Han-ZenX/CORE/docs/references/A7_Lite_硬件资料/照片/A7_Lite功能接口.png

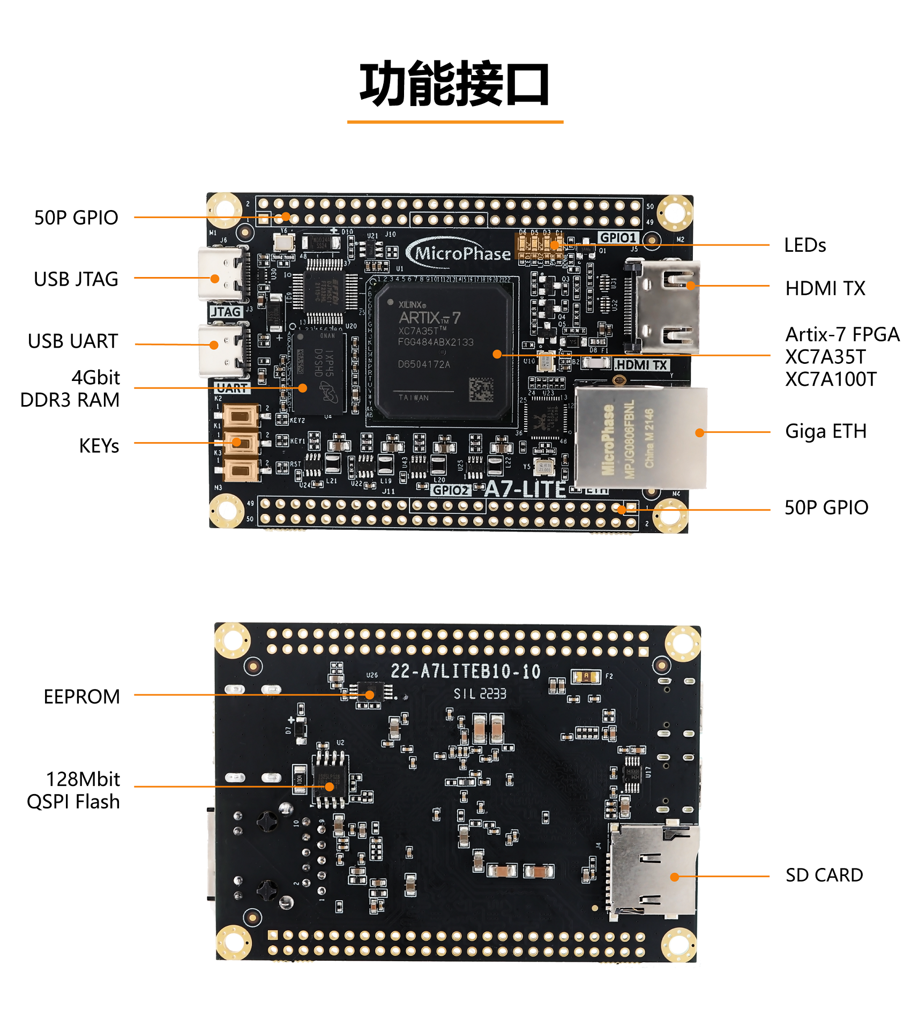
docs/references/A7_Lite_硬件资料/照片/A7_Lite功能接口.png
