Han-ZenX/CORE/docs/references/参考核心板1-1.jpg

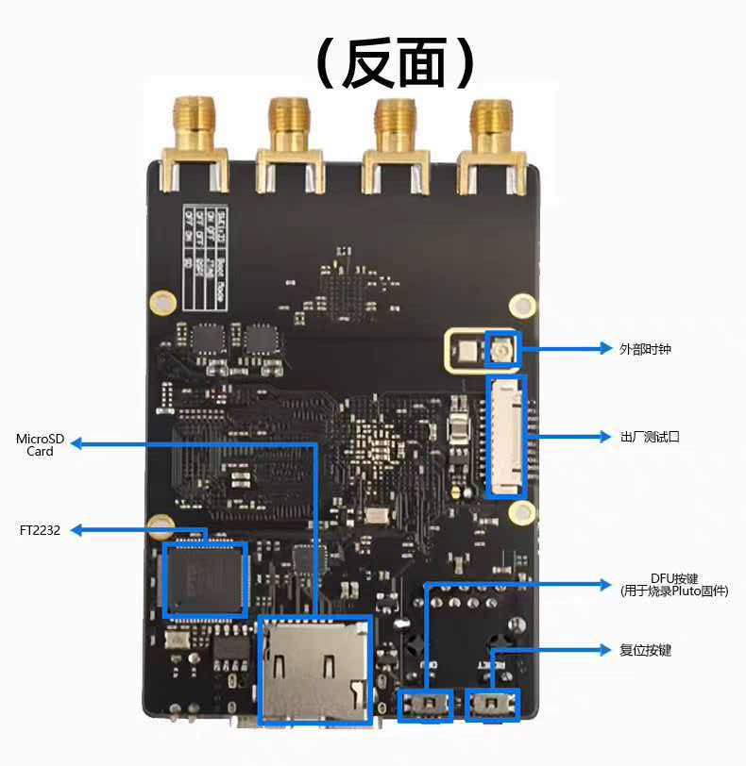
docs/references/参考核心板1-1.jpg
