Han-ZenX/CORE/docs/references/参考核心板3.jpg

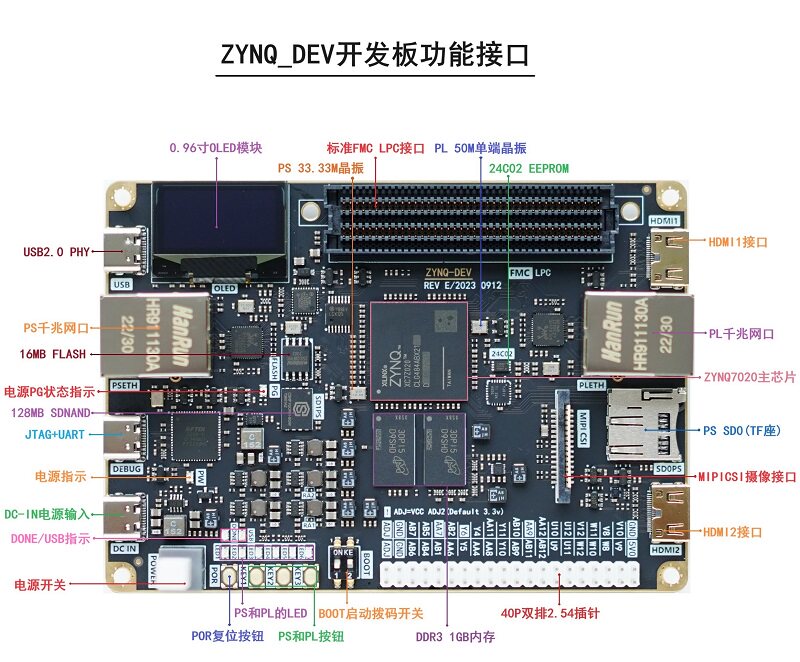
docs/references/参考核心板3.jpg
