Han-ZenX/CORE/hardware/schematic/v1.0/CORE/Comm_Periph.kicad_sch

## KiCad design hardware/schematic/v1.0/CORE/Comm_Periph.kicad_sch (2026-10-03)

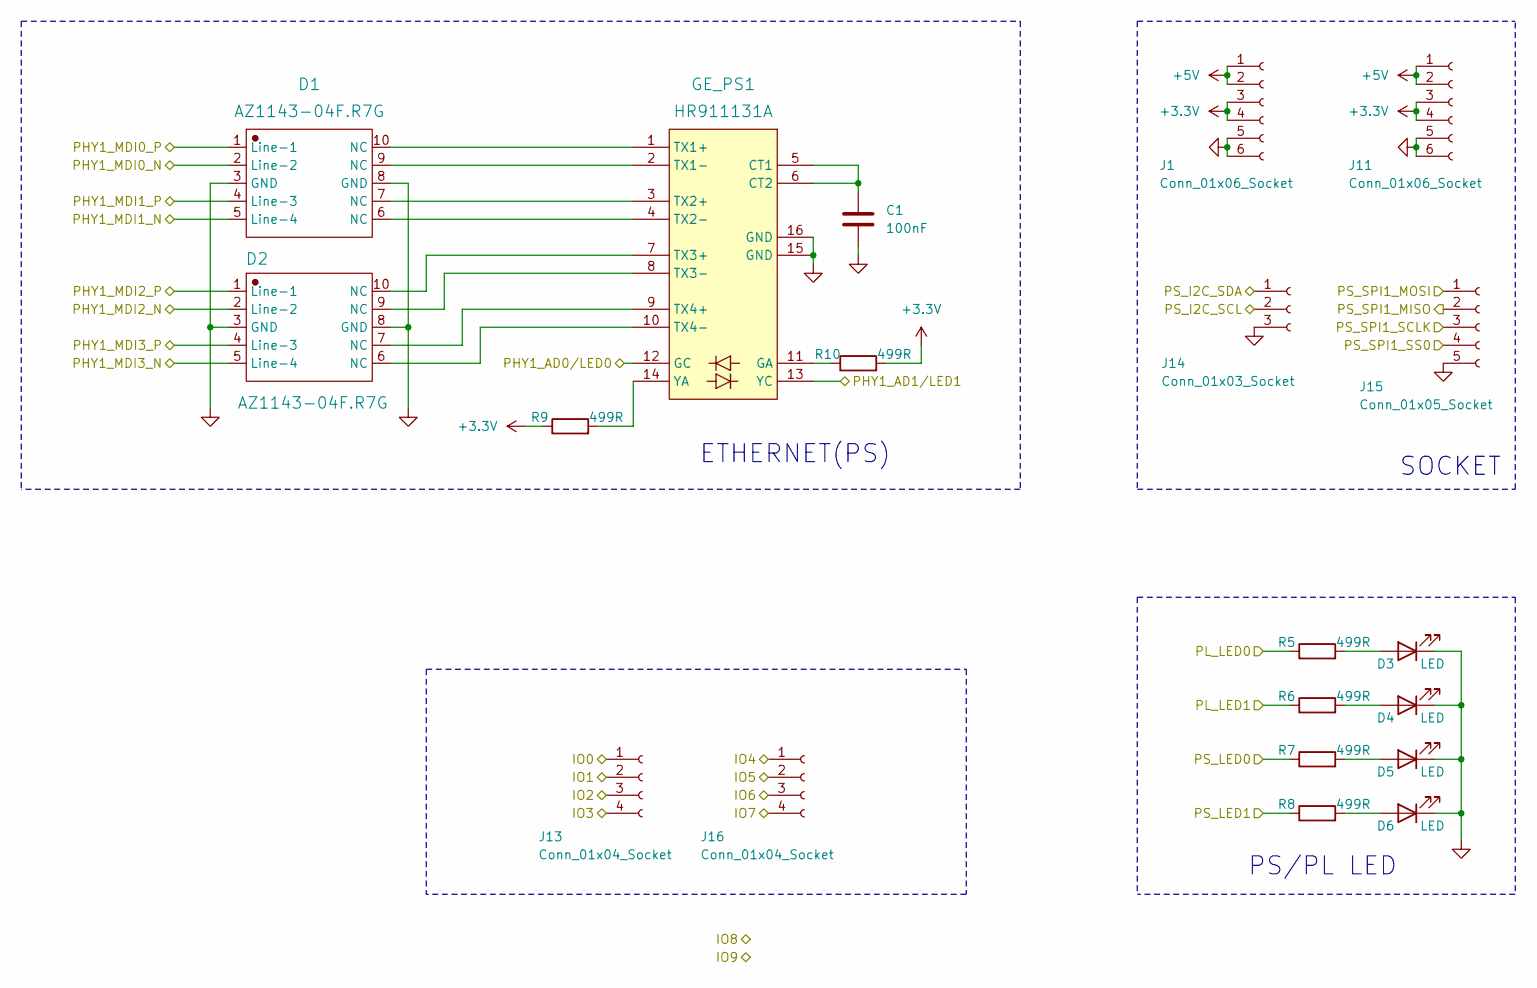
[picture p84: schematic Comm_Periph.kicad_sch]

Parts:
C1: 100nF; C_0402_1005Metric
D1, D2: AZ1143-04F.R7G; DFN2510P10E
D3, D4, D5, D6: LED; LED_0603_1608Metric
GE_PS1: HR911131A
J1, J11: Conn_01x06_Socket; PinHeader_1x06_P2.54mm_Vertical
J13, J16: Conn_01x04_Socket; PinHeader_1x04_P2.54mm_Vertical
J14: Conn_01x03_Socket; PinHeader_1x03_P2.54mm_Vertical
J15: Conn_01x05_Socket; PinHeader_1x05_P2.54mm_Vertical
R5, R6, R7, R8, R9, R10: 499R; R_0402_1005Metric

Connections:
+3.3V: J1.3, J1.4, J11.3, J11.4, R9.1, R10.2
+5V: J1.1, J1.2, J11.1, J11.2
GND: C1.2, D1.3 (GND), D1.8 (GND), D2.3 (GND), D2.8 (GND), D3.1 (K), D4.1 (K), D5.1 (K), D6.1 (K), GE_PS1.15 (GND), GE_PS1.16 (GND), J1.5, J1.6, J11.5, J11.6, J14.3, J15.5
IO0: J13.1
IO1: J13.2
IO2: J13.3
IO3: J13.4
IO4: J16.1
IO5: J16.2
IO6: J16.3
IO7: J16.4
unnamed: C1.1, GE_PS1.5 (CT1), GE_PS1.6 (CT2)
unnamed: D1.6 (NC), GE_PS1.4 (TX2-)
unnamed: D1.7 (NC), GE_PS1.3 (TX2+)
unnamed: D1.9 (NC), GE_PS1.2 (TX1-)
unnamed: D1.10 (NC), GE_PS1.1 (TX1+)
unnamed: D2.6 (NC), GE_PS1.10 (TX4-)
unnamed: D2.7 (NC), GE_PS1.9 (TX4+)
unnamed: D2.9 (NC), GE_PS1.8 (TX3-)
unnamed: D2.10 (NC), GE_PS1.7 (TX3+)
unnamed: D3.2 (A), R5.2
unnamed: D4.2 (A), R6.2
unnamed: D5.2 (A), R7.2
unnamed: D6.2 (A), R8.2
unnamed: GE_PS1.11 (GA), R10.1
unnamed: GE_PS1.14 (YA), R9.2
PHY1_AD0/LED0: GE_PS1.12 (GC)
PHY1_AD1/LED1: GE_PS1.13 (YC)
PHY1_MDI0_N: D1.2 (Line-2)
PHY1_MDI0_P: D1.1 (Line-1)
PHY1_MDI1_N: D1.5 (Line-4)
PHY1_MDI1_P: D1.4 (Line-3)
PHY1_MDI2_N: D2.2 (Line-2)
PHY1_MDI2_P: D2.1 (Line-1)
PHY1_MDI3_N: D2.5 (Line-4)
PHY1_MDI3_P: D2.4 (Line-3)
PL_LED0: R5.1
PL_LED1: R6.1
PS_I2C_SCL: J14.2
PS_I2C_SDA: J14.1
PS_LED0: R7.1
PS_LED1: R8.1
PS_SPI1_MISO: J15.2
PS_SPI1_MOSI: J15.1
PS_SPI1_SCLK: J15.3
PS_SPI1_SS0: J15.4

Notes on the sheet:
ETHERNET(PS)
PS/PL LED
SOCKET
