Han-ZenX/CORE/hardware/schematic/v1.0/CORE/Display.kicad_sch

## KiCad design hardware/schematic/v1.0/CORE/Display.kicad_sch (2026-09-08)

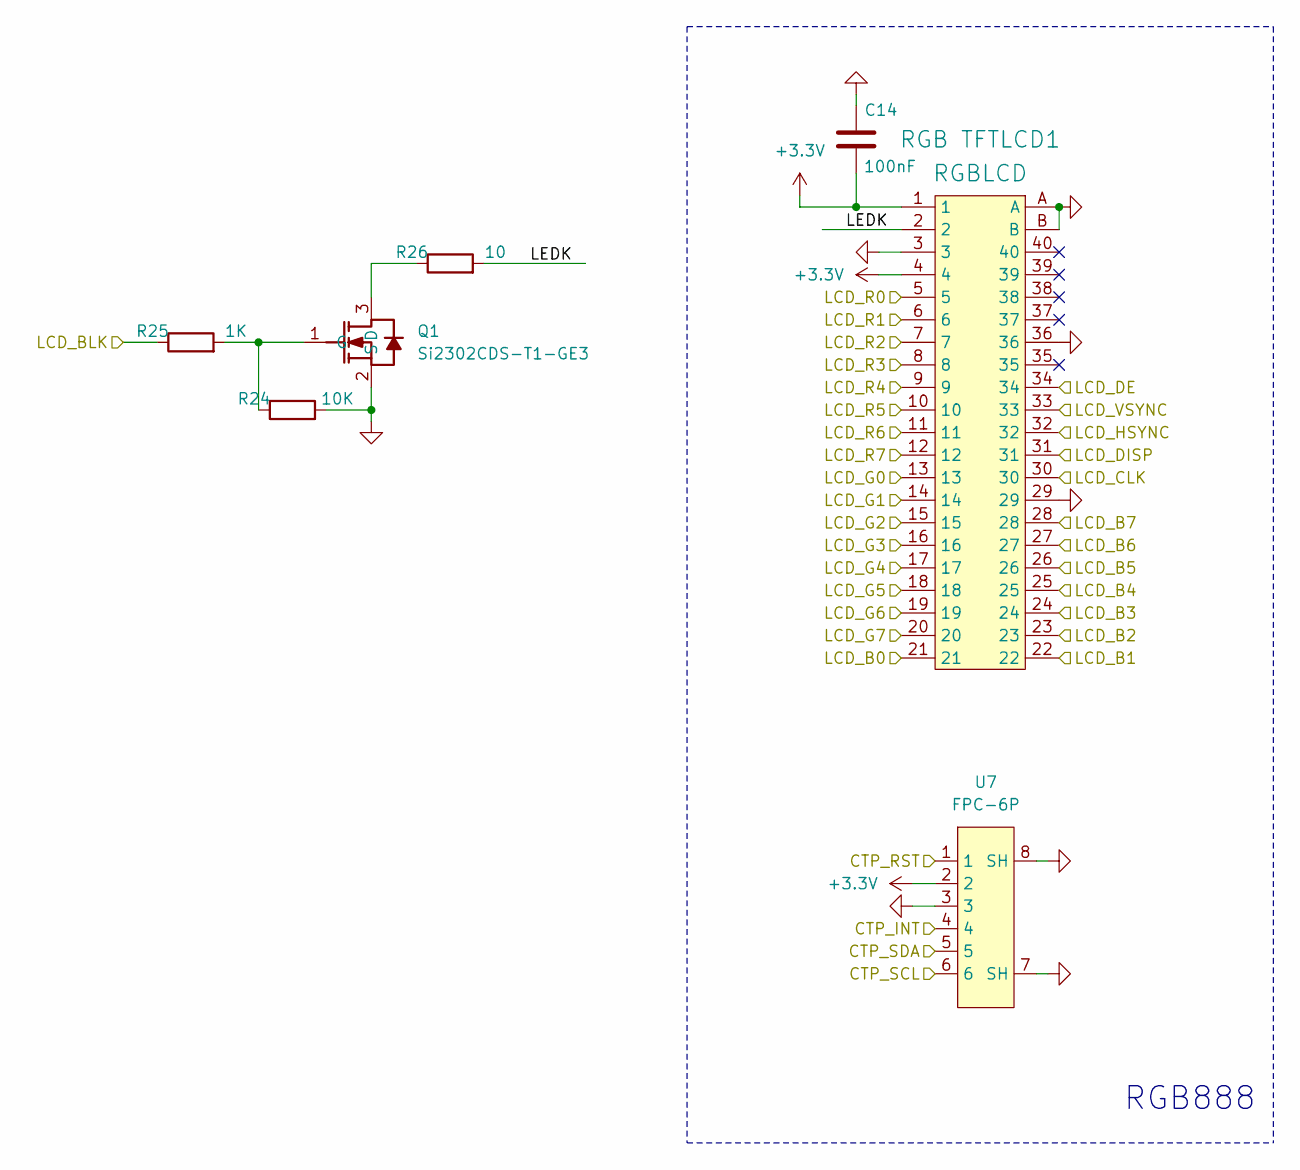
[picture p85: schematic Display.kicad_sch]

Parts:
C14: 100nF; C_0402_1005Metric
Q1: Si2302CDS-T1-GE3; Manufacturer Part Si2302CDS-T1-GE3; LCSC C10488
R24: 10K; R_0402_1005Metric
R25: 1K; R_0402_1005Metric
R26: 10; R_0402_1005Metric
RGB TFTLCD1: RGBLCD; FPC-TOP40
U7: FPC-6P

Connections:
+3.3V: C14.2, RGB TFTLCD1.1, RGB TFTLCD1.4, U7.2
CTP_INT: U7.4
CTP_RST: U7.1
CTP_SCL: U7.6
CTP_SDA: U7.5
GND: C14.1, Q1.2 (S), R24.2, RGB TFTLCD1.3, RGB TFTLCD1.29, RGB TFTLCD1.36, RGB TFTLCD1.A, RGB TFTLCD1.B, U7.3, U7.7 (SH), U7.8 (SH)
LCD_B0: RGB TFTLCD1.21
LCD_B1: RGB TFTLCD1.22
LCD_B2: RGB TFTLCD1.23
LCD_B3: RGB TFTLCD1.24
LCD_B4: RGB TFTLCD1.25
LCD_B5: RGB TFTLCD1.26
LCD_B6: RGB TFTLCD1.27
LCD_B7: RGB TFTLCD1.28
LCD_BLK: R25.1
LCD_CLK: RGB TFTLCD1.30
LCD_DE: RGB TFTLCD1.34
LCD_DISP: RGB TFTLCD1.31
LCD_G0: RGB TFTLCD1.13
LCD_G1: RGB TFTLCD1.14
LCD_G2: RGB TFTLCD1.15
LCD_G3: RGB TFTLCD1.16
LCD_G4: RGB TFTLCD1.17
LCD_G5: RGB TFTLCD1.18
LCD_G6: RGB TFTLCD1.19
LCD_G7: RGB TFTLCD1.20
LCD_HSYNC: RGB TFTLCD1.32
LCD_R0: RGB TFTLCD1.5
LCD_R1: RGB TFTLCD1.6
LCD_R2: RGB TFTLCD1.7
LCD_R3: RGB TFTLCD1.8
LCD_R4: RGB TFTLCD1.9
LCD_R5: RGB TFTLCD1.10
LCD_R6: RGB TFTLCD1.11
LCD_R7: RGB TFTLCD1.12
LCD_VSYNC: RGB TFTLCD1.33
LEDK: R26.2, RGB TFTLCD1.2
unnamed: Q1.1 (G), R24.1, R25.2
unnamed: Q1.3 (D), R26.1

Notes on the sheet:
RGB888
