Han-ZenX/CORE/hardware/schematic/v1.0/CORE/Power.kicad_sch

## KiCad design hardware/schematic/v1.0/CORE/Power.kicad_sch (2026-10-03)

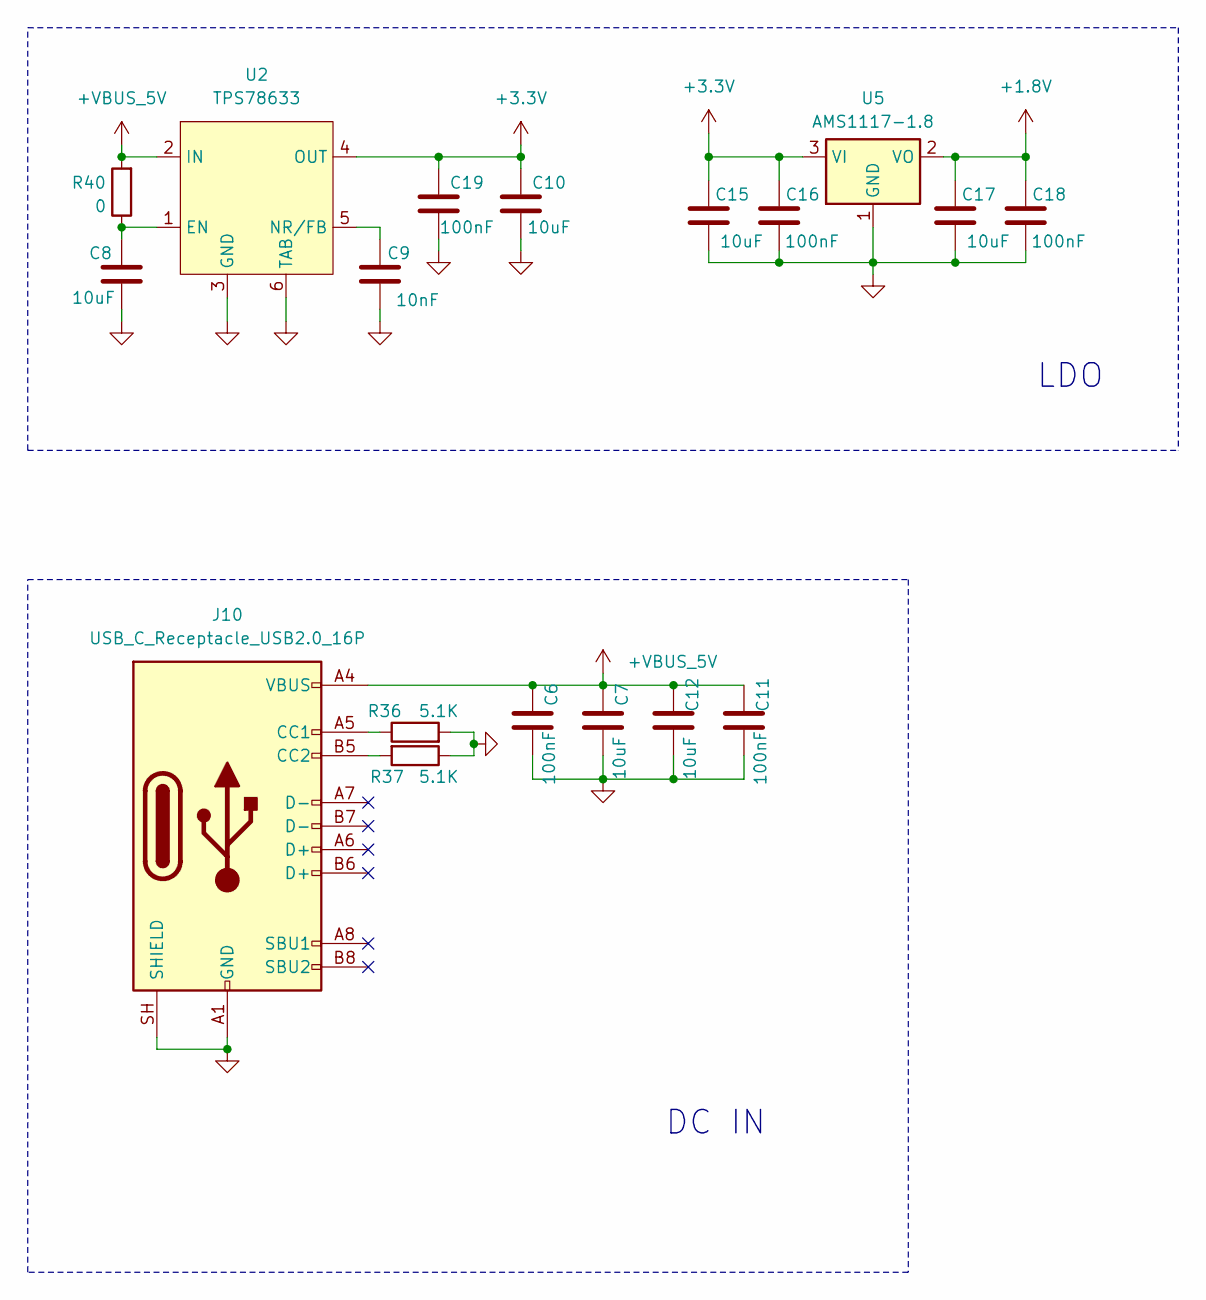
[picture p86: schematic Power.kicad_sch]

Parts:
C6, C11, C19: 100nF; C_0402_1005Metric
C7, C8, C10, C12, C15, C17: 10uF; C_0603_1608Metric
C9: 10nF; C_0402_1005Metric
C16, C18: 100nF; C_0603_1608Metric
J10: USB_C_Receptacle_USB2.0_16P; USB_C_Receptacle_Palconn_UTC16-G
R36, R37: 5.1K; R_0402_1005Metric
R40: 0; R_0402_1005Metric
U2: TPS78633; SOT-223-6
U5: AMS1117-1.8; SOT-223-3_TabPin2

Connections:
+1.8V: C17.1, C18.1, U5.2 (VO)
+3.3V: C10.2, C15.1, C16.1, C19.2, U2.4 (OUT), U5.3 (VI)
+VBUS_5V: C6.1, C7.1, C11.1, C12.1, J10.A4 (VBUS), J10.A9 (VBUS), J10.B4 (VBUS), J10.B9 (VBUS), R40.2, U2.2 (IN)
GND: C6.2, C7.2, C8.1, C9.1, C10.1, C11.2, C12.2, C15.2, C16.2, C17.2, C18.2, C19.1, J10.A1 (GND), J10.A12 (GND), J10.B1 (GND), J10.B12 (GND), J10.SH (SHIELD), R36.2, R37.1, U2.3 (GND), U2.6 (TAB), U5.1 (GND)
unnamed: C8.2, R40.1, U2.1 (EN)
unnamed: C9.2, U2.5 (NR/FB)
unnamed: J10.A5 (CC1), R36.1
unnamed: J10.B5 (CC2), R37.2

Notes on the sheet:
DC IN
LDO
