Han-ZenX/CORE/hardware/schematic/v1.0/CORE/Signal.kicad_sch

## KiCad design hardware/schematic/v1.0/CORE/Signal.kicad_sch (2026-10-02)

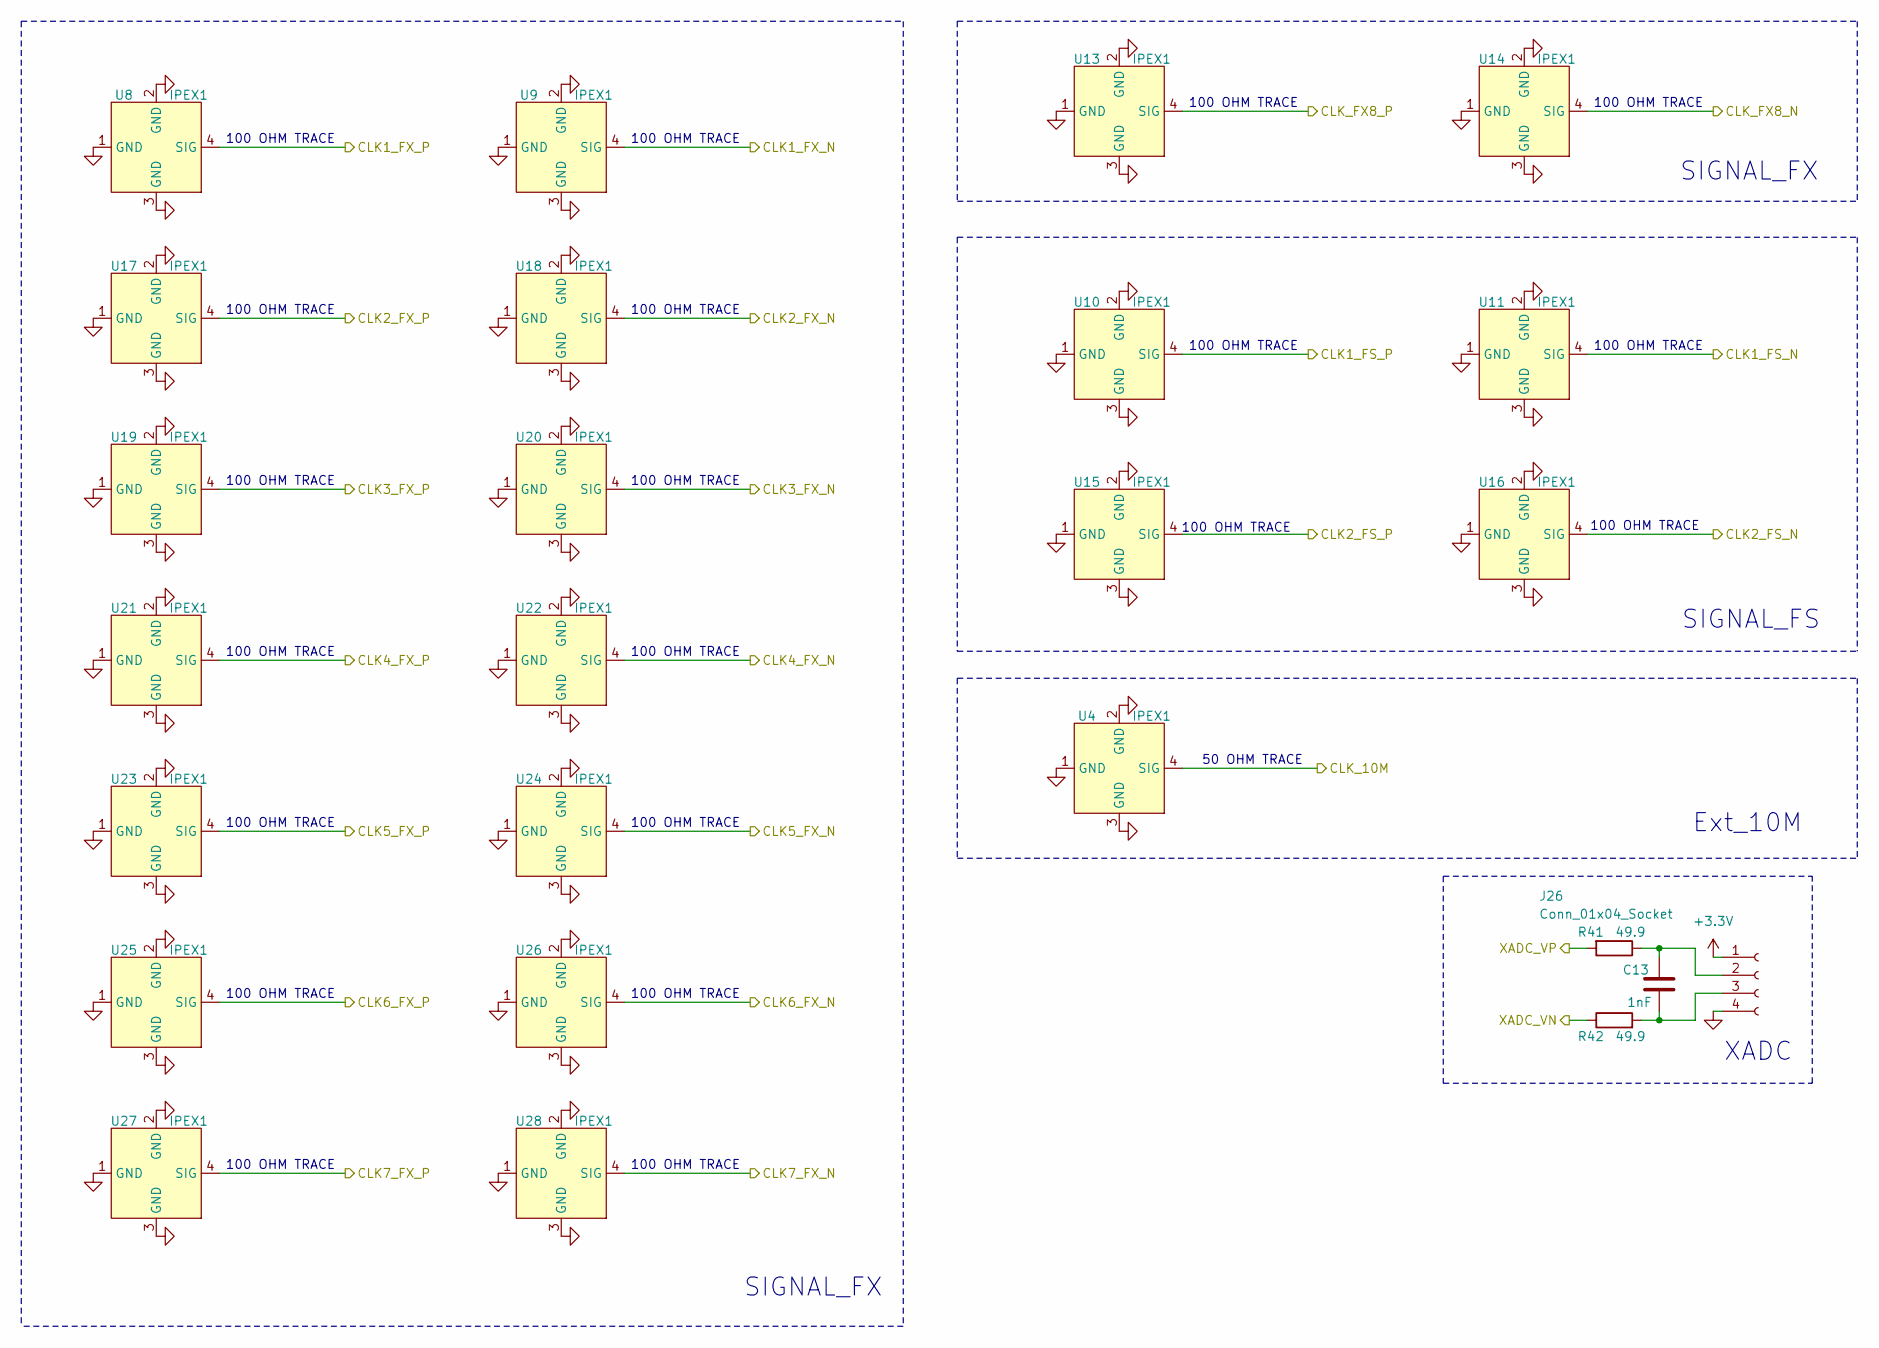
[picture p87: schematic Signal.kicad_sch]

Parts:
C13: 1nF; C_0402_1005Metric
J26: Conn_01x04_Socket; PinHeader_1x04_P2.54mm_Vertical
R41, R42: 49.9; R_0402_1005Metric
U4, U8, U9, U10, U11, U13, U14, U15, U16, U17, U18, U19, U20, U21, U22, U23, U24, U25, U26, U27, U28: IPEX1; JLC_IPEX-1

Connections:
+3.3V: J26.1
CLK1_FS_N: U11.4 (SIG)
CLK1_FS_P: U10.4 (SIG)
CLK1_FX_N: U9.4 (SIG)
CLK1_FX_P: U8.4 (SIG)
CLK2_FS_N: U16.4 (SIG)
CLK2_FS_P: U15.4 (SIG)
CLK2_FX_N: U18.4 (SIG)
CLK2_FX_P: U17.4 (SIG)
CLK3_FX_N: U20.4 (SIG)
CLK3_FX_P: U19.4 (SIG)
CLK4_FX_N: U22.4 (SIG)
CLK4_FX_P: U21.4 (SIG)
CLK5_FX_N: U24.4 (SIG)
CLK5_FX_P: U23.4 (SIG)
CLK6_FX_N: U26.4 (SIG)
CLK6_FX_P: U25.4 (SIG)
CLK7_FX_N: U28.4 (SIG)
CLK7_FX_P: U27.4 (SIG)
CLK_10M: U4.4 (SIG)
CLK_FX8_N: U14.4 (SIG)
CLK_FX8_P: U13.4 (SIG)
GND: J26.4, U4.1 (GND), U4.2 (GND), U4.3 (GND), U8.1 (GND), U8.2 (GND), U8.3 (GND), U9.1 (GND), U9.2 (GND), U9.3 (GND), U10.1 (GND), U10.2 (GND), U10.3 (GND), U11.1 (GND), U11.2 (GND), U11.3 (GND), U13.1 (GND), U13.2 (GND), U13.3 (GND), U14.1 (GND), U14.2 (GND), U14.3 (GND), U15.1 (GND), U15.2 (GND), U15.3 (GND), U16.1 (GND), U16.2 (GND), U16.3 (GND), U17.1 (GND), U17.2 (GND), U17.3 (GND), U18.1 (GND), U18.2 (GND), U18.3 (GND), U19.1 (GND), U19.2 (GND), U19.3 (GND), U20.1 (GND), U20.2 (GND), U20.3 (GND), U21.1 (GND), U21.2 (GND), U21.3 (GND), U22.1 (GND), U22.2 (GND), U22.3 (GND), U23.1 (GND), U23.2 (GND), U23.3 (GND), U24.1 (GND), U24.2 (GND), U24.3 (GND), U25.1 (GND), U25.2 (GND), U25.3 (GND), U26.1 (GND), U26.2 (GND), U26.3 (GND), U27.1 (GND), U27.2 (GND), U27.3 (GND), U28.1 (GND), U28.2 (GND), U28.3 (GND)
unnamed: C13.1, J26.2, R41.1
unnamed: C13.2, J26.3, R42.2
XADC_VN: R42.1
XADC_VP: R41.2

Notes on the sheet:
100 OHM TRACE
SIGNAL_FX
SIGNAL_FS
XADC
50 OHM TRACE
Ext_10M
