Han-ZenX/CORE/hardware/schematic/v1.0/CORE/Storage.kicad_sch

## KiCad design hardware/schematic/v1.0/CORE/Storage.kicad_sch (2026-10-03)

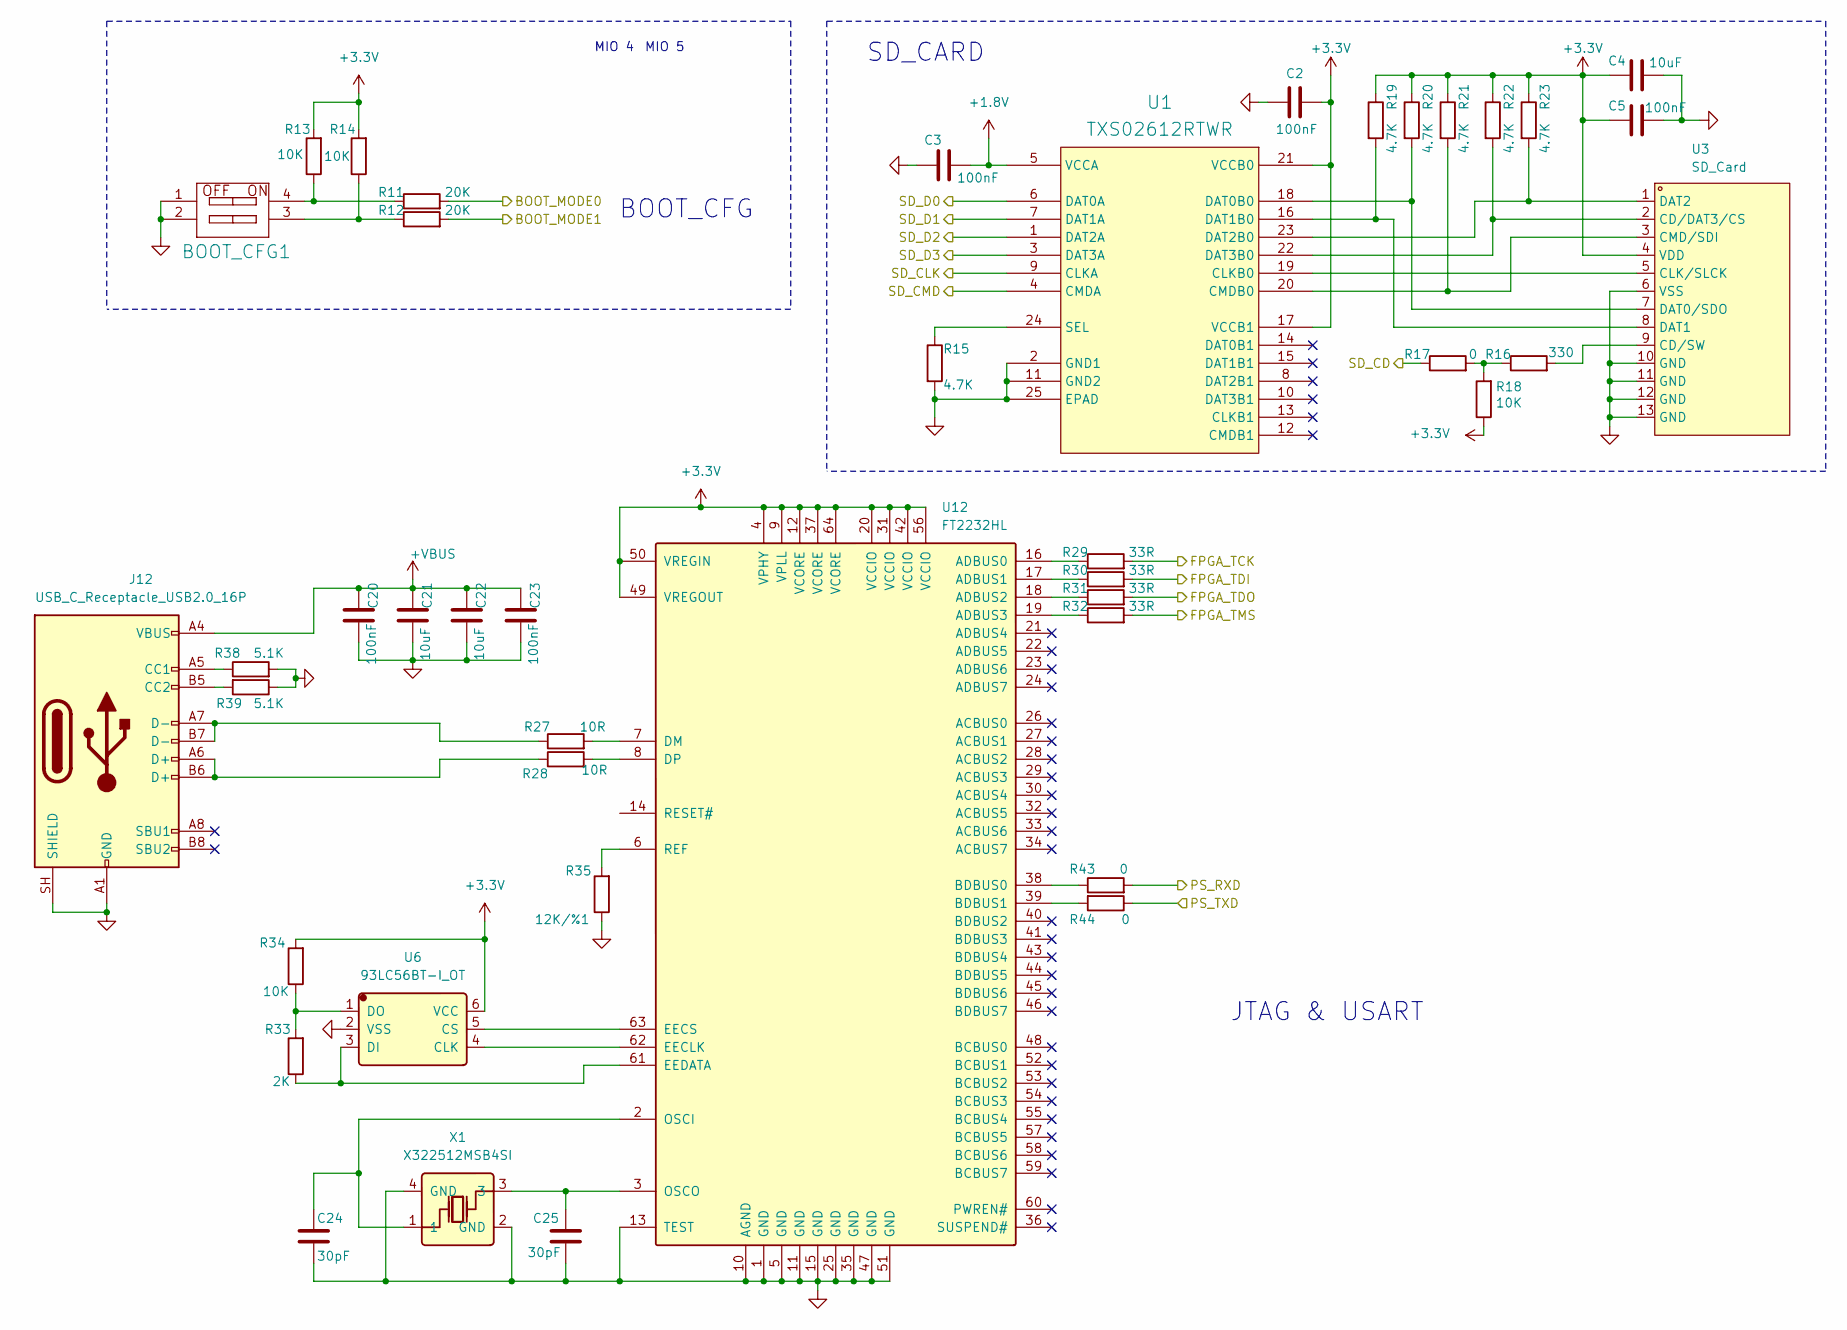
[picture p88: schematic Storage.kicad_sch]

Parts:
BOOT_CFG1: CSW-2P; CSW DIP-2P
C2, C3, C5, C20, C23: 100nF; C_0402_1005Metric
C4: 10uF; C_0402_1005Metric
C21, C22: 10uF; C_0603_1608Metric
C24, C25: 30pF; C_0402_1005Metric
J12: USB_C_Receptacle_USB2.0_16P; USB_C_Receptacle_Palconn_UTC16-G
R11, R12: 20K; R_0402_1005Metric
R13, R14, R18, R34: 10K; R_0402_1005Metric
R15, R19, R20, R21, R22, R23: 4.7K; R_0402_1005Metric
R16: 330; R_0402_1005Metric
R17, R43, R44: 0; R_0402_1005Metric
R27, R28: 10R; R_0402_1005Metric
R29, R30, R31, R32: 33R; R_0402_1005Metric
R33: 2K; R_0402_1005Metric
R35: 12K/%1; R_0402_1005Metric
R38, R39: 5.1K; R_0402_1005Metric
U1: TXS02612RTWR; QFN24_RTW
U3: SD_Card; SIM-SMD_LX_XDFP-0090-012
U6: 93LC56BT-I_OT; Manufacturer Part 93LC56BT-I/OT; LCSC C190271
U12: FT2232HL; Manufacturer Part FT2232HL-REEL; LCSC C27882
X1: X322512MSB4SI; Manufacturer Part X322512MSB4SI; LCSC C9002

Connections:
+1.8V: C3.2, U1.5 (VCCA)
+3.3V: C2.2, C4.1, C5.1, R13.2, R14.2, R18.1, R19.1, R20.1, R21.1, R22.1, R23.1, R34.2, U1.17 (VCCB1), U1.21 (VCCB0), U3.4 (VDD), U6.6 (VCC), U12.4 (VPHY), U12.9 (VPLL), U12.12 (VCORE), U12.20 (VCCIO), U12.31 (VCCIO), U12.37 (VCORE), U12.42 (VCCIO), U12.49 (VREGOUT), U12.50 (VREGIN), U12.56 (VCCIO), U12.64 (VCORE)
+VBUS: C20.1, C21.1, C22.1, C23.1, J12.A4 (VBUS), J12.A9 (VBUS), J12.B4 (VBUS), J12.B9 (VBUS)
BOOT_MODE0: R11.2
BOOT_MODE1: R12.2
FPGA_TCK: R29.2
FPGA_TDI: R30.2
FPGA_TDO: R31.2
FPGA_TMS: R32.2
GND: BOOT_CFG1.1, BOOT_CFG1.2, C2.1, C3.1, C4.2, C5.2, C20.2, C21.2, C22.2, C23.2, C24.1, C25.1, J12.A1 (GND), J12.A12 (GND), J12.B1 (GND), J12.B12 (GND), J12.SH (SHIELD), R15.2, R35.1, R38.2, R39.1, U1.2 (GND1), U1.11 (GND2), U1.25 (EPAD), U3.6 (VSS), U3.10 (GND), U3.11 (GND), U3.12 (GND), U3.13 (GND), U6.2 (VSS), U12.1 (GND), U12.5 (GND), U12.10 (AGND), U12.11 (GND), U12.13 (TEST), U12.15 (GND), U12.25 (GND), U12.35 (GND), U12.47 (GND), U12.51 (GND), X1.2 (GND), X1.4 (GND)
unnamed: BOOT_CFG1.3, R12.1, R14.1
unnamed: BOOT_CFG1.4, R11.1, R13.1
unnamed: C24.2, U12.2 (OSCI), X1.1
unnamed: C25.2, U12.3 (OSCO), X1.3
unnamed: J12.A5 (CC1), R38.1
unnamed: J12.A6 (D+), J12.B6 (D+), R28.1
unnamed: J12.A7 (D-), J12.B7 (D-), R27.1
unnamed: J12.B5 (CC2), R39.2
unnamed: R15.1, U1.24 (SEL)
unnamed: R16.1, R17.2, R18.2
unnamed: R16.2, U3.9 (CD/SW)
unnamed: R19.2, U1.16 (DAT1B0), U3.8 (DAT1)
unnamed: R20.2, U1.18 (DAT0B0), U3.7 (DAT0/SDO)
unnamed: R21.2, U1.20 (CMDB0), U3.3 (CMD/SDI)
unnamed: R22.2, U1.22 (DAT3B0), U3.2 (CD/DAT3/CS)
unnamed: R23.2, U1.23 (DAT2B0), U3.1 (DAT2)
unnamed: R27.2, U12.7 (DM)
unnamed: R28.2, U12.8 (DP)
unnamed: R29.1, U12.16 (ADBUS0)
unnamed: R30.1, U12.17 (ADBUS1)
unnamed: R31.1, U12.18 (ADBUS2)
unnamed: R32.1, U12.19 (ADBUS3)
unnamed: R33.1, U6.3 (DI), U12.61 (EEDATA)
unnamed: R33.2, R34.1, U6.1 (DO)
unnamed: R35.2, U12.6 (REF)
unnamed: R43.1, U12.38 (BDBUS0)
unnamed: R44.2, U12.39 (BDBUS1)
unnamed: U1.19 (CLKB0), U3.5 (CLK/SLCK)
unnamed: U6.4 (CLK), U12.62 (EECLK)
unnamed: U6.5 (CS), U12.63 (EECS)
PS_RXD: R43.2
PS_TXD: R44.1
SD_CD: R17.1
SD_CLK: U1.9 (CLKA)
SD_CMD: U1.4 (CMDA)
SD_D0: U1.6 (DAT0A)
SD_D1: U1.7 (DAT1A)
SD_D2: U1.1 (DAT2A)
SD_D3: U1.3 (DAT3A)

Notes on the sheet:
BOOT_CFG
MIO 5
JTAG & USART
MIO 4
SD_CARD
